WILDERNESSWIRELESS/WILDERNESS-WIRELESS-I/resources/MOSFET_high_side_driver_HV.png

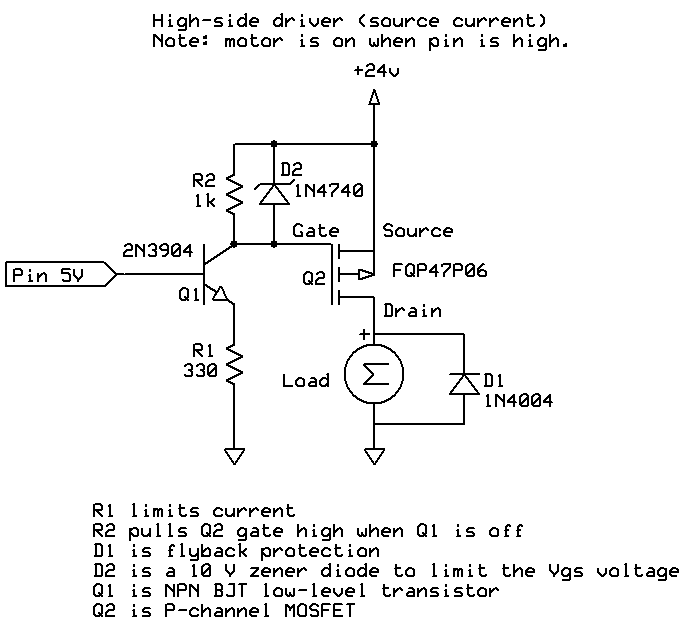
resources/MOSFET_high_side_driver_HV.png
