WILDERNESSWIRELESS/WILDERNESS-WIRELESS-I/resources/MOSFET_low_side_driver.png

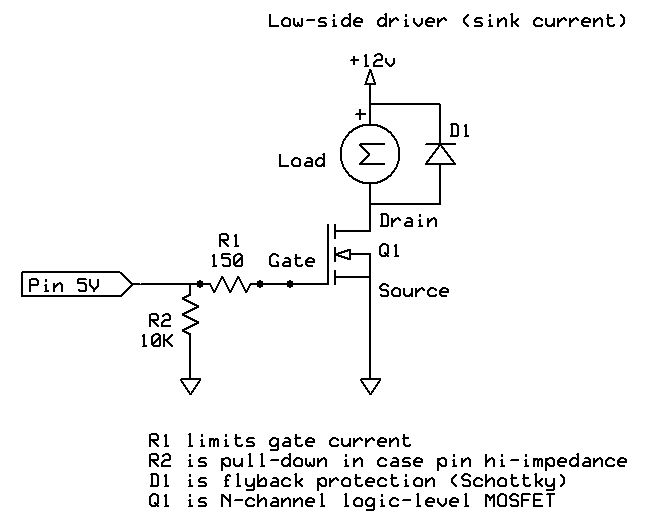
resources/MOSFET_low_side_driver.png
