WILDERNESSWIRELESS/WILDERNESS-WIRELESS-I/wilderness/wilderness-wireless/dns-liar.lua

--Thanks to Thomas Shaddack for optimizations - 20150707 ARe
dns_ip=wifi.ap.getip()
local i1,i2,i3,i4=dns_ip:match("(%d+)%.(%d+)%.(%d+)%.(%d+)")
x00=string.char(0)
x01=string.char(1)
dns_str1=string.char(128)..x00..x00..x01..x00..x01..x00..x00..x00..x00
dns_str2=x00..x01..x00..x01..string.char(192)..string.char(12)..x00..x01..x00..x01..x00..x00..string.char(3)..x00..x00..string.char(4)
dns_strIP=string.char(i1)..string.char(i2)..string.char(i3)..string.char(i4)
svr=net.createServer(net.UDP)
svr:on("receive",function(svr,dns_pl)
  decodedns(dns_pl)
  svr:send(dns_tr..dns_str1..dns_q..dns_str2..dns_strIP)
  collectgarbage("collect")
end)
svr:listen(53)
function decodedns(dns_pl)
  local a=string.len(dns_pl)
  dns_tr = string.sub(dns_pl, 1, 2)
  local bte=""
  dns_q=""
  local i=13
  local bte2=""
  while bte2 ~= "0" do
    bte = string.byte(dns_pl,i)
    bte2 = string.format("%x", bte )
    dns_q = dns_q .. string.char(bte)
    i=i+1
  end
end
print("DNS Server is now listening. Free Heap:", node.heap())
